manubompella/thingBaseBoard/Reference/WhatsApp Image 2017-02-03 at 10.37.23.jpeg

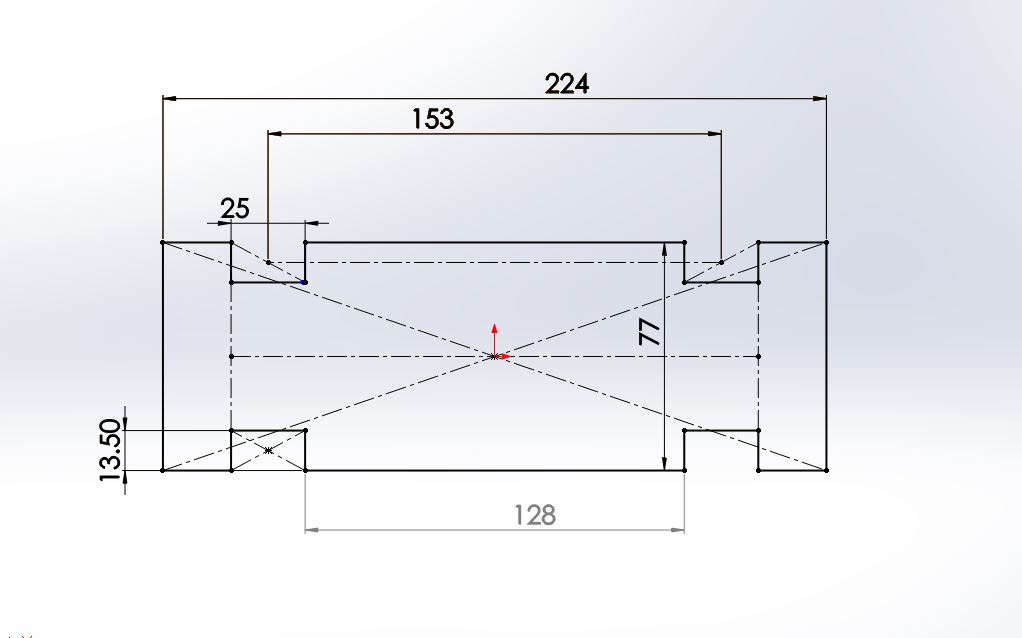
Reference/WhatsApp Image 2017-02-03 at 10.37.23.jpeg
