manubompella/thingBaseBoard/Reference/WhatsApp Image 2017-02-16 at 08.44.42.jpeg

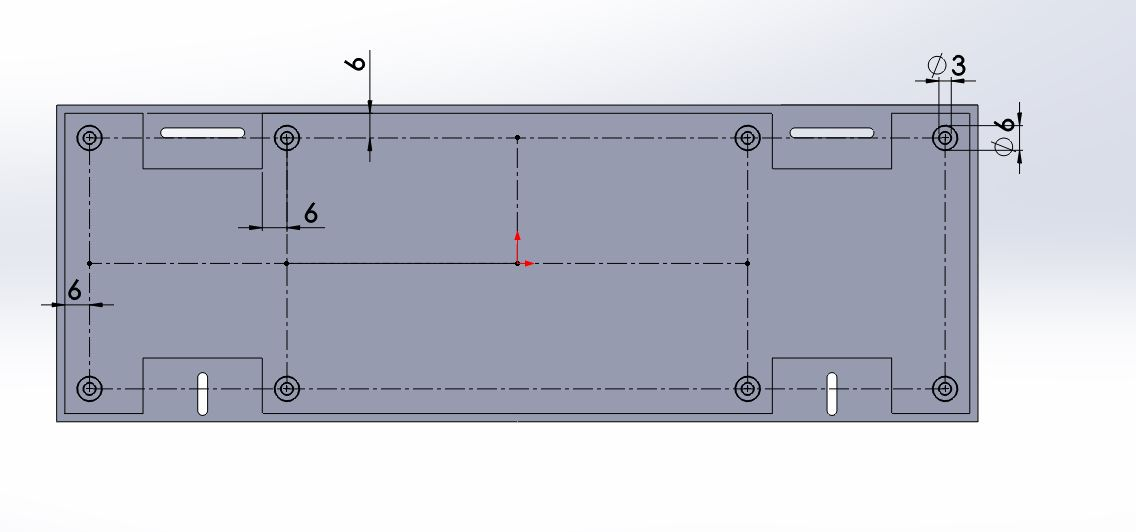
Reference/WhatsApp Image 2017-02-16 at 08.44.42.jpeg
